calstar/ellie-ground/Calibration/Flow Meter Calibration Files/MatLabCdMeasurementCalc/Oct32022CdTest/OCt32022CdCalcr1.xls

Time(ms) | PT 2 | PT 3 | PT 4 | volume flow (m^3/s) | break Interval | mass flow (kg/s) | Cd Value | Reynolds Num
2075 | 137895.15 | 101352.93 | 0 | 0 | 1050 | 0 | 0 | 0
3125 | 137895.15 | 101352.93 | 0 | 0 | 1050 | 0 | 0 | 0
4175 | 137895.15 | 101352.93 | 0 | 0 | 1050 | 0 | 0 | 0
4503 | 137895.15 | 101352.93 | 0 | 3.499239381e-06 | 328 | 0.003499239381 | 0 | 1.292703316e-07
4566 | 137895.15 | 101352.93 | 0 | 9.917990395e-06 | 63 | 0.009917990395 | 0 | 3.663944554e-07
4633 | 137895.15 | 101352.93 | 0 | 1.789682177e-05 | 67 | 0.01789682177 | 0 | 6.611517056e-07
4695 | 137895.15 | 101352.93 | 0 | 2.812016238e-05 | 62 | 0.02812016238 | 0 | 1.038826533e-06
4752 | 137895.15 | 101352.93 | 0 | 3.895757001e-05 | 57 | 0.03895757001 | 0 | 1.439186476e-06
4806 | 137895.15 | 101352.93 | 0 | 4.967108693e-05 | 54 | 0.04967108693 | 0 | 1.834969597e-06
4859 | 137895.15 | 101352.93 | 0 | 5.973249429e-05 | 53 | 0.05973249429 | 0 | 2.206662221e-06
4914 | 137895.15 | 101352.93 | 0 | 7.192731323e-05 | 55 | 0.07192731323 | 0 | 2.657168207e-06
4968 | 137895.15 | 101352.93 | 0 | 7.931766371e-05 | 54 | 0.07931766371 | 0 | 2.930185556e-06
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
