calstar/ellie-ground/Calibration/Flow Meter Calibration Files/MatLabCdMeasurementCalc/Oct32022CdTest/OCt32022CdCalcr2.xls

Time(ms) | PT 2 | PT 3 | PT 4 | volume flow (m^3/s) | break Interval | mass flow (kg/s) | Cd Value | Reynolds Num
4075 | 137895.15 | 101352.93 | 0 | 0 | 2050 | 0 | 0 | 0
6125 | 137895.15 | 101352.93 | 0 | 0 | 2050 | 0 | 0 | 0
8175 | 137895.15 | 101352.93 | 0 | 0 | 2050 | 0 | 0 | 0
8641 | 137895.15 | 101352.93 | 0 | 4.409600475e-05 | 466 | 0.04409600475 | 0 | 1.629012633e-06
8716 | 137895.15 | 101352.93 | 0 | 0.0001655294417 | 75 | 0.1655294417 | 0 | 6.1150563e-06
8787 | 137895.15 | 101352.93 | 0 | 0.0002653648218 | 71 | 0.2653648218 | 0 | 9.803215721e-06
8850 | 137895.15 | 101352.93 | 0 | 0.0003489301191 | 63 | 0.3489301191 | 0 | 1.289031909e-05
8911 | 137895.15 | 101352.93 | 0 | 0.0004213509752 | 61 | 0.4213509752 | 0 | 1.556571996e-05
8973 | 137895.15 | 101352.93 | 0 | 0.0004833589514 | 62 | 0.4833589514 | 0 | 1.785644397e-05
9033 | 137895.15 | 101352.93 | 0 | 0.0005332515604 | 60 | 0.5332515604 | 0 | 1.969959712e-05
9091 | 137895.15 | 101352.93 | 0 | 0.0005587710277 | 58 | 0.5587710277 | 0 | 2.064234771e-05
9148 | 137895.15 | 101352.93 | 0 | 0.0005754865111 | 57 | 0.5754865111 | 0 | 2.125985794e-05
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
