calstar/ellie-ground/Calibration/Flow Meter Calibration Files/MatLabCdMeasurementCalc/Oct32022CdTest/OCt32022CdCalcr3.xls

Time(ms) | PT 2 | PT 3 | PT 4 | volume flow (m^3/s) | break Interval | mass flow (kg/s) | Cd Value | Reynolds Num
4075 | 137895.15 | 101352.93 | 0 | 0 | 2050 | 0 | 0 | 0
5894 | 137895.15 | 101352.93 | 0 | 4.142494664e-05 | 1819 | 5.260968223e-05 | 0.01015786496 | 1.943528386e-09
6062 | 137895.15 | 101352.93 | 0 | 3.997073106e-05 | 168 | 5.076282844e-05 | 0.009801274869 | 1.875301159e-09
6194 | 137895.15 | 101352.93 | 0 | 7.002451974e-05 | 132 | 8.893114007e-05 | 0.01717080342 | 3.285330529e-09
6299 | 137895.15 | 101352.93 | 0 | 0.0001073493863 | 105 | 0.0001363337207 | 0.02632328243 | 5.036496038e-09
6388 | 137895.15 | 101352.93 | 0 | 0.0001479260406 | 89 | 0.0001878660715 | 0.0362731365 | 6.940225208e-09
6471 | 137895.15 | 101352.93 | 0 | 0.0001819183298 | 83 | 0.0002310362788 | 0.04460842988 | 8.535036653e-09
6541 | 137895.15 | 101352.93 | 0 | 0.0002122346852 | 70 | 0.0002695380502 | 0.05204234276 | 9.957384828e-09
6612 | 137895.15 | 101352.93 | 0 | 0.0002406726788 | 71 | 0.000305654302 | 0.0590156601 | 1.129160617e-08
6684 | 137895.15 | 101352.93 | 0 | 0.0002612942636 | 72 | 0.0003318437148 | 0.0640723057 | 1.225910616e-08
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
