calstar/ellie-ground/Calibration/Flow Meter Calibration Files/MatLabCdMeasurementCalc/Sep102022CdTest/Sep102022CdCalcr1.xls

Time(ms) | PT 2 | PT 3 | PT 4 | volume flow (m^3/s) | break Interval | mass flow (kg/s) | Cd Value | Reynolds Num
2476 | 117210.87 | 101352.93 | 0 | 0 | 1050 | 0 | 0 | 0
3526 | 117210.87 | 101352.93 | 0 | 0 | 1050 | 0 | 0 | 0
4576 | 117210.87 | 101352.93 | 0 | 0 | 1050 | 0 | 0 | 0
5626 | 117210.87 | 101352.93 | 0 | 0 | 1050 | 0 | 0 | 0
6676 | 117210.87 | 101352.93 | 0 | 0 | 1050 | 0 | 0 | 0
7726 | 117210.87 | 101352.93 | 0 | 0 | 1050 | 0 | 0 | 0
8776 | 117210.87 | 101352.93 | 0 | 0 | 1050 | 0 | 0 | 0
9826 | 117210.87 | 101352.93 | 0 | 0 | 1050 | 0 | 0 | 0
10876 | 117210.87 | 101352.93 | 0 | 0 | 1050 | 0 | 0 | 0
11926 | 117210.87 | 101352.93 | 0 | 0 | 1050 | 0 | 0 | 0
12976 | 117210.87 | 101352.93 | 0 | 0 | 1050 | 0 | 0 | 0
14026 | 117210.87 | 101352.93 | 0 | 0 | 1050 | 0 | 0 | 0
15076 | 117210.87 | 101352.93 | 0 | 0 | 1050 | 0 | 0 | 0
16126 | 117210.87 | 101352.93 | 0 | 0 | 1050 | 0 | 0 | 0
17176 | 117210.87 | 101352.93 | 0 | 0 | 1050 | 0 | 0 | 0
18226 | 117210.87 | 101352.93 | 0 | 0 | 1050 | 0 | 0 | 0
19276 | 117210.87 | 101352.93 | 0 | 0 | 1050 | 0 | 0 | 0
20326 | 117210.87 | 101352.93 | 0 | 0 | 1050 | 0 | 0 | 0
21376 | 117210.87 | 101352.93 | 0 | 0 | 1050 | 0 | 0 | 0
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
