calstar/ellie-ground/PCB Design/ellie_board/EllieBoard.kicad_sch

## KiCad design PCB Design/ellie_board/EllieBoard.kicad_sch (2022-04-06)

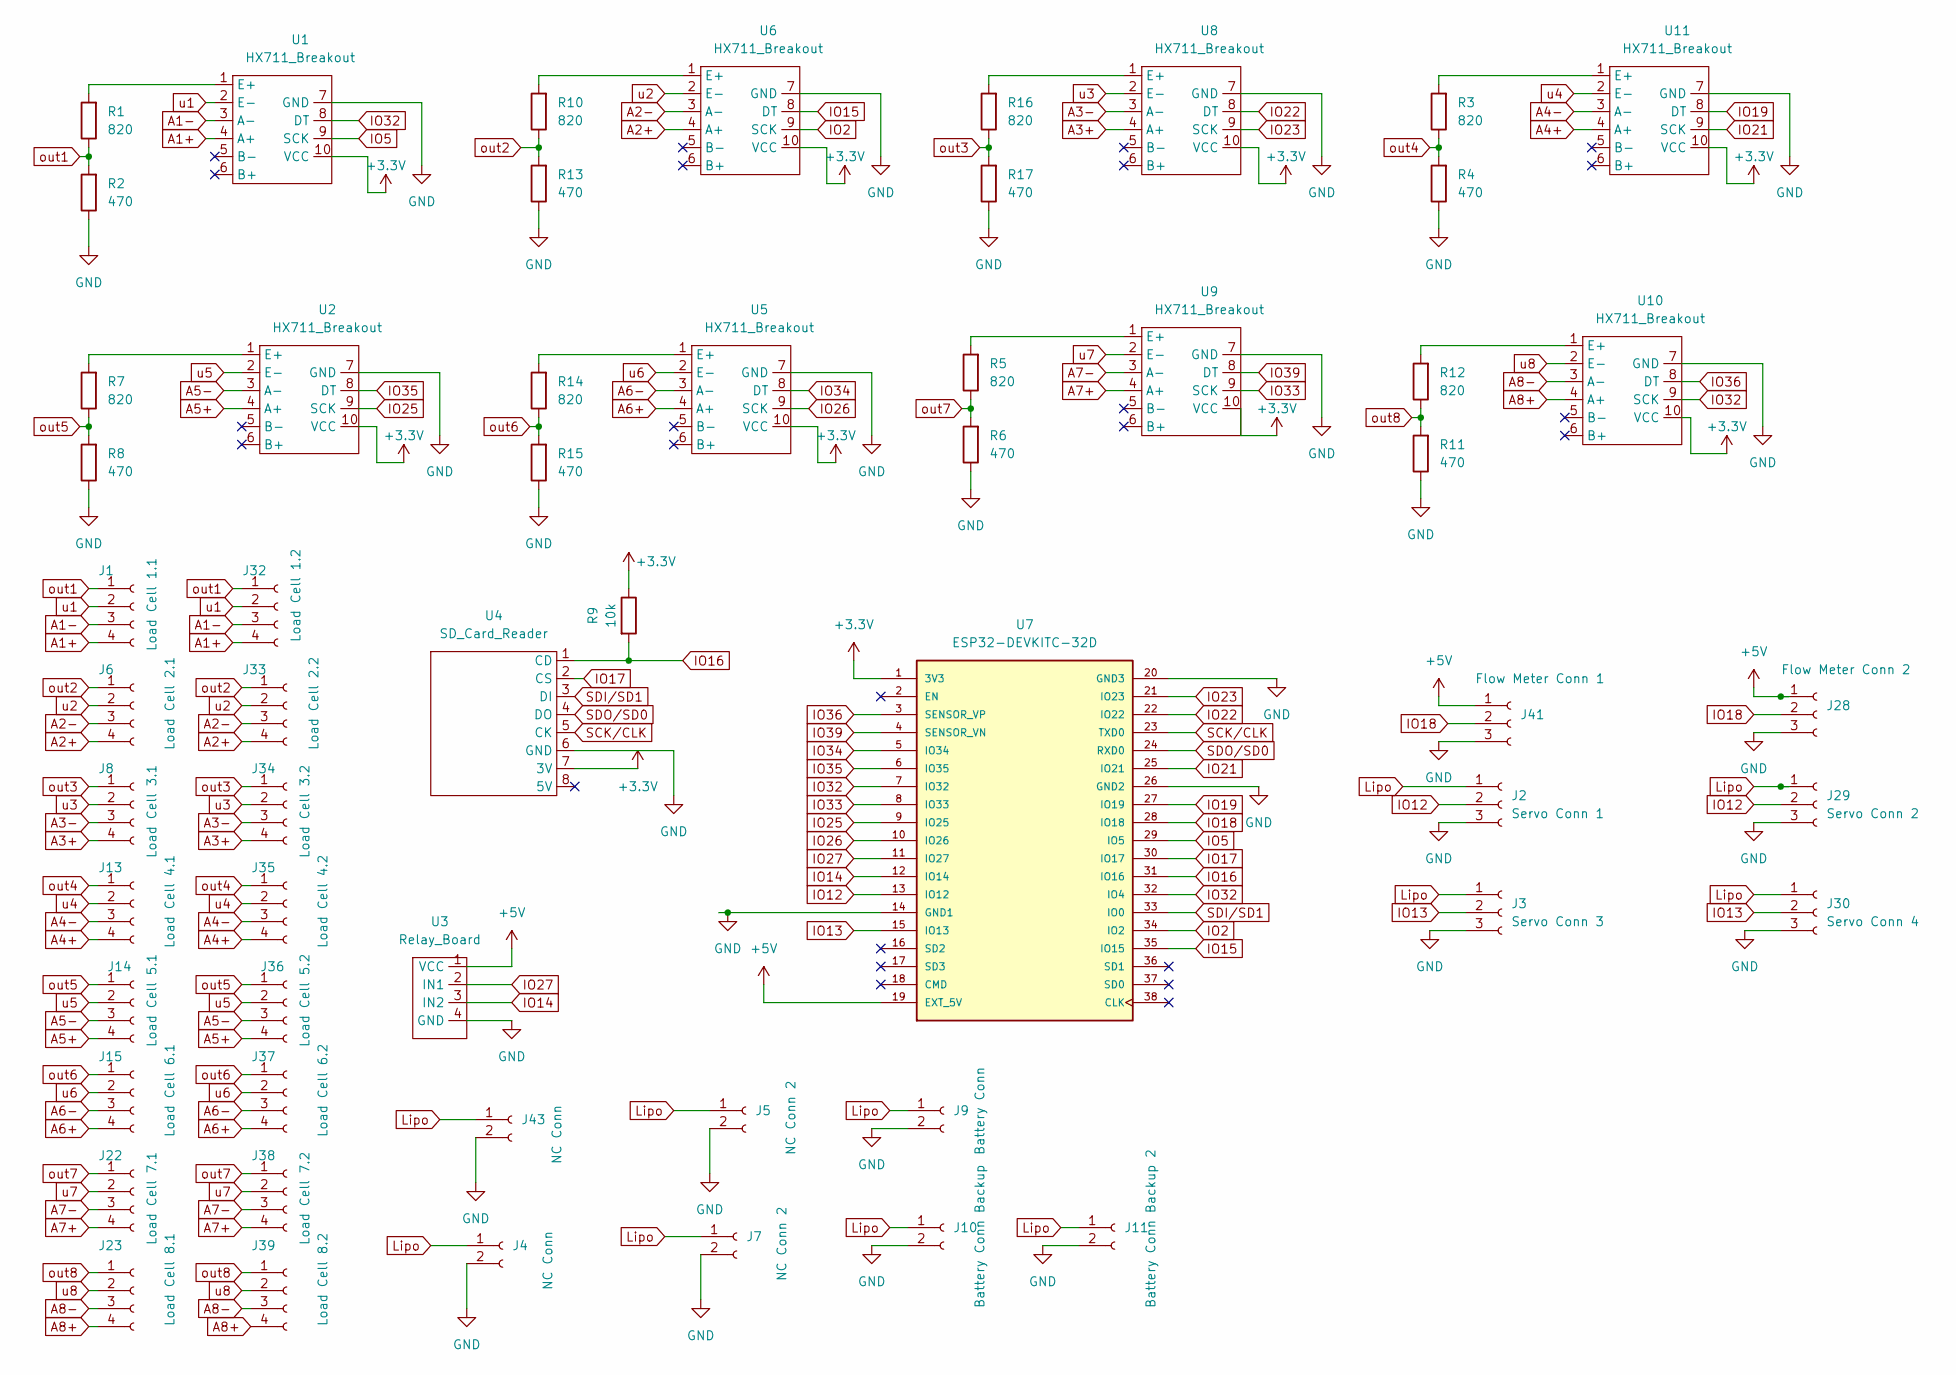
[picture p6: schematic EllieBoard.kicad_sch]

Parts:
J1: Load Cell 1.1; JST_XH_B4B-XH-AM_1x04_P2.50mm_Vertical
J2: Servo Conn 1; JST_XH_B3B-XH-AM_1x03_P2.50mm_Vertical
J3: Servo Conn 3; JST_XH_B3B-XH-AM_1x03_P2.50mm_Vertical
J4, J43: NC Conn; JST_XH_B2B-XH-AM_1x02_P2.50mm_Vertical
J5, J7: NC Conn 2; TerminalBlock_Phoenix_MPT-0,5-2-2.54_1x02_P2.54mm_Horizontal
J6: Load Cell 2.1; JST_XH_B4B-XH-AM_1x04_P2.50mm_Vertical
J8: Load Cell 3.1; JST_XH_B4B-XH-AM_1x04_P2.50mm_Vertical
J9: Battery Conn; DEANS
J10: Battery Conn Backup; JST_XH_B2B-XH-AM_1x02_P2.50mm_Vertical
J11: Battery Conn Backup 2; TerminalBlock_Phoenix_MPT-0,5-2-2.54_1x02_P2.54mm_Horizontal
J13: Load Cell 4.1; JST_XH_B4B-XH-AM_1x04_P2.50mm_Vertical
J14: Load Cell 5.1; JST_XH_B4B-XH-AM_1x04_P2.50mm_Vertical
J15: Load Cell 6.1; JST_XH_B4B-XH-AM_1x04_P2.50mm_Vertical
J22: Load Cell 7.1; JST_XH_B4B-XH-AM_1x04_P2.50mm_Vertical
J23: Load Cell 8.1; JST_XH_B4B-XH-AM_1x04_P2.50mm_Vertical
J28: Flow Meter Conn 2; TerminalBlock_Phoenix_MPT-0,5-3-2.54_1x03_P2.54mm_Horizontal
J29: Servo Conn 2; TerminalBlock_Phoenix_MPT-0,5-3-2.54_1x03_P2.54mm_Horizontal
J30: Servo Conn 4; TerminalBlock_Phoenix_MPT-0,5-3-2.54_1x03_P2.54mm_Horizontal
J32: Load Cell 1.2; TerminalBlock_Phoenix_MPT-0,5-4-2.54_1x04_P2.54mm_Horizontal
J33: Load Cell 2.2; TerminalBlock_Phoenix_MPT-0,5-4-2.54_1x04_P2.54mm_Horizontal
J34: Load Cell 3.2; TerminalBlock_Phoenix_MPT-0,5-4-2.54_1x04_P2.54mm_Horizontal
J35: Load Cell 4.2; TerminalBlock_Phoenix_MPT-0,5-4-2.54_1x04_P2.54mm_Horizontal
J36: Load Cell 5.2; TerminalBlock_Phoenix_MPT-0,5-4-2.54_1x04_P2.54mm_Horizontal
J37: Load Cell 6.2; TerminalBlock_Phoenix_MPT-0,5-4-2.54_1x04_P2.54mm_Horizontal
J38: Load Cell 7.2; TerminalBlock_Phoenix_MPT-0,5-4-2.54_1x04_P2.54mm_Horizontal
J39: Load Cell 8.2; TerminalBlock_Phoenix_MPT-0,5-4-2.54_1x04_P2.54mm_Horizontal
J41: Flow Meter Conn 1; JST_XH_B3B-XH-AM_1x03_P2.50mm_Vertical
R1, R3, R5, R7, R10, R12, R14, R16: 820; R_1206_3216Metric
R2, R4, R6, R8, R11, R13, R15, R17: 470; R_1206_3216Metric
R9: 10k; R_1206_3216Metric
U1, U2, U5, U6, U8, U9, U10, U11: HX711_Breakout; HX711_Breakout_Board
U3: Relay_Board; Relay_Breakout
U4: SD_Card_Reader; SD_Card_Breakout
U7: ESP32-DEVKITC-32D; MODULE_ESP32-DEVKITC-32D; PARTREV 4

Connections:
+3.3V: R9.1, U1.10 (VCC), U2.10 (VCC), U4.7 (3V), U5.10 (VCC), U6.10 (VCC), U7.1 (3V3), U8.10 (VCC), U9.10 (VCC), U10.10 (VCC), U11.10 (VCC)
+5V: J28.1, J41.1, U3.1 (VCC), U7.19 (EXT_5V)
A1+: J1.4, J32.4, U1.4 (A+)
A1-: J1.3, J32.3, U1.3 (A-)
A2+: J6.4, J33.4, U6.4 (A+)
A2-: J6.3, J33.3, U6.3 (A-)
A3+: J8.4, J34.4, U8.4 (A+)
A3-: J8.3, J34.3, U8.3 (A-)
A4+: J13.4, J35.4, U11.4 (A+)
A4-: J13.3, J35.3, U11.3 (A-)
A5+: J14.4, J36.4, U2.4 (A+)
A5-: J14.3, J36.3, U2.3 (A-)
A6+: J15.4, J37.4, U5.4 (A+)
A6-: J15.3, J37.3, U5.3 (A-)
A7+: J22.4, J38.4, U9.4 (A+)
A7-: J22.3, J38.3, U9.3 (A-)
A8+: J23.4, J39.4, U10.4 (A+)
A8-: J23.3, J39.3, U10.3 (A-)
GND: J2.3, J3.3, J4.2, J5.2, J7.2, J9.2, J10.2, J11.2, J28.3, J29.3, J30.3, J41.3, J43.2, R2.1, R4.1, R6.1, R8.1, R11.1, R13.1, R15.1, R17.1, U1.7 (GND), U2.7 (GND), U3.4 (GND), U4.6 (GND), U5.7 (GND), U6.7 (GND), U7.14 (GND1), U7.20 (GND3), U7.26 (GND2), U8.7 (GND), U9.7 (GND), U10.7 (GND), U11.7 (GND)
IO2: U6.9 (SCK), U7.34 (IO2)
IO5: U1.9 (SCK), U7.29 (IO5)
IO12: J2.2, J29.2, U7.13 (IO12)
IO13: J3.2, J30.2, U7.15 (IO13)
IO14: U3.3 (IN2), U7.12 (IO14)
IO15: U6.8 (DT), U7.35 (IO15)
IO16: R9.2, U4.1 (CD), U7.31 (IO16)
IO17: U4.2 (CS), U7.30 (IO17)
IO18: J28.2, J41.2, U7.28 (IO18)
IO19: U7.27 (IO19), U11.8 (DT)
IO21: U7.25 (IO21), U11.9 (SCK)
IO22: U7.22 (IO22), U8.8 (DT)
IO23: U7.21 (IO23), U8.9 (SCK)
IO25: U2.9 (SCK), U7.9 (IO25)
IO26: U5.9 (SCK), U7.10 (IO26)
IO27: U3.2 (IN1), U7.11 (IO27)
IO32: U1.8 (DT), U7.7 (IO32), U7.32 (IO4), U10.9 (SCK)
IO33: U7.8 (IO33), U9.9 (SCK)
IO34: U5.8 (DT), U7.5 (IO34)
IO35: U2.8 (DT), U7.6 (IO35)
IO36: U7.3 (SENSOR_VP), U10.8 (DT)
IO39: U7.4 (SENSOR_VN), U9.8 (DT)
Lipo: J2.1, J3.1, J4.1, J5.1, J7.1, J9.1, J10.1, J11.1, J29.1, J30.1, J43.1
unnamed: R1.2, U1.1 (E+)
unnamed: R3.2, U11.1 (E+)
unnamed: R5.2, U9.1 (E+)
unnamed: R7.2, U2.1 (E+)
unnamed: R10.2, U6.1 (E+)
unnamed: R12.2, U10.1 (E+)
unnamed: R14.2, U5.1 (E+)
unnamed: R16.2, U8.1 (E+)
SCK/CLK: U4.5 (CK), U7.23 (TXD0)
SDI/SD1: U4.3 (DI), U7.33 (IO0)
SDO/SD0: U4.4 (DO), U7.24 (RXD0)
out1: J1.1, J32.1, R1.1, R2.2
out2: J6.1, J33.1, R10.1, R13.2
out3: J8.1, J34.1, R16.1, R17.2
out4: J13.1, J35.1, R3.1, R4.2
out5: J14.1, J36.1, R7.1, R8.2
out6: J15.1, J37.1, R14.1, R15.2
out7: J22.1, J38.1, R5.1, R6.2
out8: J23.1, J39.1, R11.2, R12.1
u1: J1.2, J32.2, U1.2 (E-)
u2: J6.2, J33.2, U6.2 (E-)
u3: J8.2, J34.2, U8.2 (E-)
u4: J13.2, J35.2, U11.2 (E-)
u5: J14.2, J36.2, U2.2 (E-)
u6: J15.2, J37.2, U5.2 (E-)
u7: J22.2, J38.2, U9.2 (E-)
u8: J23.2, J39.2, U10.2 (E-)
