calstar/ellie-ground/sensor_board/sensor_board.kicad_sch

## KiCad design sensor_board/sensor_board.kicad_sch (2022-04-04)

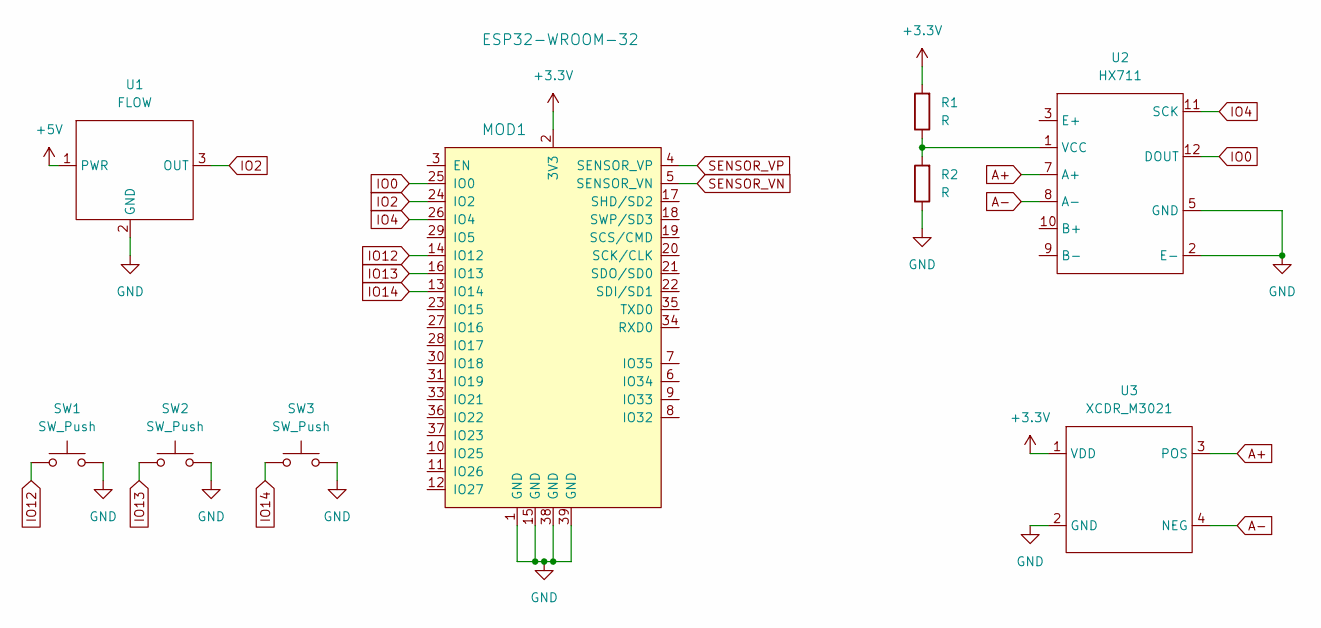
[picture p7: schematic sensor_board.kicad_sch]

Parts:
MOD1: ESP32-WROOM-32; ESP32-WROOM-32D; MPN ESP32-WROOM-32; Digi-Key_PN 1904-1010-1-ND
R1, R2: R
SW1, SW2, SW3: SW_Push
U1: FLOW
U2: HX711
U3: XCDR_M3021

Connections:
+3.3V: MOD1.2 (3V3), R1.2, U3.1 (VDD)
+5V: U1.1 (PWR)
A+: U2.7 (A+), U3.3 (POS)
A-: U2.8 (A-), U3.4 (NEG)
GND: MOD1.1 (GND), MOD1.15 (GND), MOD1.38 (GND), MOD1.39 (GND), R2.1, SW1.2, SW2.2, SW3.2, U1.2 (GND), U2.2 (E-), U2.5 (GND), U3.2 (GND)
IO0: MOD1.25 (IO0), U2.12 (DOUT)
IO2: MOD1.24 (IO2), U1.3 (OUT)
IO4: MOD1.26 (IO4), U2.11 (SCK)
IO12: MOD1.14 (IO12), SW1.1
IO13: MOD1.16 (IO13), SW2.1
IO14: MOD1.13 (IO14), SW3.1
unnamed: R1.1, R2.2, U2.1 (VCC)
SENSOR_VN: MOD1.5 (SENSOR_VN)
SENSOR_VP: MOD1.4 (SENSOR_VP)
