calstar/ellie-ground/Aurduino/Main.Stable/COMBoard/COMBoard.ino

#include <esp_now.h>
#include <WiFi.h>
#include <ESP32Servo.h>
#include <Wire.h>
#include <Arduino.h>
#include "HX711.h"


int servo1ClosedPosition = 100;
int servo1OpenPosition = 0;
int servo2ClosedPosition = 130;
int servo2OpenPosition = 20;
//EH VENT SEFRVO 1 =180

float pressTime = 0;
const int buttonpin1 = 19;
//const int buttonpin1 = 27;
const int buttonpin2 = 17;
const int igniterIndicator = 16;
const int firePin = 21; //SET PIN NUMBER BUTTON

const int pin6 = 4;
const int LEDpin = 23;
const int servo1Open = 22;//SET PIN NUMBER BASED ON SOLDERING//
const int servo2Open = 14;//SET PIN NUMBER BASED ON SOLDERING//
const int DAQIndicator = 25;//SET PIN NUMBER BASED ON SOLDERING//
const int COMIndicator = 5;//SET PIN NUMBER BASED ON SOLDERING//


String success;
String message;
int servo1_curr = servo1ClosedPosition;
int servo2_curr = servo2ClosedPosition;
float incomingS1 = 0;
float incomingS2 = 0;
float incomingPT1 = 0;
float incomingPT2 = 0;
float incomingPT3 = 0;
float incomingPT4 = 0;
float incomingFM = 0;
float incomingLC1 = 0;
float incomingLC2 = 0;
float incomingLC3 = 0;
esp_now_peer_info_t peerInfo;
bool pressed1 = false;
bool pressed2 = false;
bool pressed3 = false;

// SET FOR ACTIVE MODE //
bool hotfire = true;
//SET IF PLOTTING WITH MATLAB OR NOT. SERVO MANUAL CONTROL AND
//MATLAB PLOTTING ARE NOT COMPATIBLE DUE TO USING THE SAME SERIAL
//INPUT. IF TRUE, PLOTTING ENABLED. IF FALSE, MANUAL CONTROL ENABLED
bool MatlabPlot = true;


float button1Time = 0;
float currTime = 0;
float loopTime = 0;

float receiveTimeDAQ = 0;
float receiveTimeCOM = 0;

const int delayOpenServoTime = 250;
const int servoOnTime = 1500;
const int delayCloseServoTime = 0;

//for blinking LED during Data Collection
int x = 1;
unsigned long t1;
unsigned long t2;

int state = 0;
//

//DAQ Breadboard {0x24, 0x62, 0xAB, 0xD2, 0x85, 0xDC}
//DAQ Protoboard {0x0C, 0xDC, 0x7E, 0xCB, 0x05, 0xC4}
//NON BUSTED DAQ {0x7C, 0x9E, 0xBD, 0xD8, 0xFC, 0x14}
// uint8_t broadcastAddress[] = {0x7C, 0x9E, 0xBD, 0xD8, 0xFC, 0x14}; //change to new Mac Address

uint8_t broadcastAddress[] = {0x30, 0xC6, 0xF7, 0x2A, 0x28, 0x04};
//Structure example to send data
//Must match the receiver structure
typedef struct struct_message {
    float pt1;
    float pt2;
    float pt3;
    float pt4;
    float lc1;
    float lc2;
    float lc3;
    float fm;
    int S1;
    int S2;
    int S1S2;
    boolean I;
} struct_message;

// Create a struct_message called Readings to recieve sensor readings remotely
struct_message incomingReadings;

// Create a struct_message to send commands
struct_message Commands;

//
void OnDataSent(const uint8_t *mac_addr, esp_now_send_status_t status) {
 // Serial.print("\r\nLast Packet Send Status:\t");
 // Serial.println(status == ESP_NOW_SEND_SUCCESS ? "Delivery Success" : "Delivery Fail");
  if (status == 0){
    success = "Delivery Success :)";
    digitalWrite(DAQIndicator, HIGH);
    receiveTimeDAQ = millis();
  }
  else{
    success = "Delivery Fail :(";
    digitalWrite(DAQIndicator, LOW);
  }

}

void OnDataRecv(const uint8_t * mac, const uint8_t *incomingData, int len) {
  memcpy(&incomingReadings, incomingData, sizeof(incomingReadings));
 // Serial.print("Bytes received: ");
  // Serial.println(len);
  incomingPT1 = incomingReadings.pt1;
  incomingPT2 = incomingReadings.pt2;
  incomingPT3 = incomingReadings.pt3;
  incomingPT4 = incomingReadings.pt4;
  incomingFM = incomingReadings.fm;
  incomingLC1 = incomingReadings.lc1;
  incomingLC2 = incomingReadings.lc2;
  incomingLC3 = incomingReadings.lc3;
  incomingS1 = incomingReadings.S1;
  incomingS2 = incomingReadings.S2;
  digitalWrite(COMIndicator, HIGH);
  receiveTimeCOM = millis();
  // Serial.println("Data received");

}

void printLine(String string) {
  // a = 10;
  Serial.println(string);
}

void setup() {
  Commands.S1 = servo1ClosedPosition;
  Commands.S2 = servo2ClosedPosition;
  // put your setup code here, to run once:
  Serial.begin(115200);
  pinMode(buttonpin1,INPUT);
  pinMode(buttonpin2, INPUT);
  pinMode(igniterIndicator,INPUT);
  pinMode(firePin, INPUT);

  pinMode(LEDpin, OUTPUT);
  pinMode(servo1Open, OUTPUT);
  pinMode(servo2Open, OUTPUT);
  pinMode(DAQIndicator, OUTPUT);
  pinMode(COMIndicator, OUTPUT);
  pinMode(pin6, OUTPUT);

  digitalWrite(LEDpin,LOW);
  digitalWrite(servo1Open, LOW);
  digitalWrite(servo2Open, LOW);
  digitalWrite(DAQIndicator, LOW);
  digitalWrite(COMIndicator, LOW);
  digitalWrite(pin6, LOW);


  //set device as WiFi station
  WiFi.mode(WIFI_STA);

  //initialize ESP32
   if (esp_now_init() != ESP_OK) {
    //Serial.println("Error initializing ESP-NOW");
    return;
  }
   // Once ESPNow is successfully Init, we will register for Send CB to
  // get the status of Trasnmitted packet
  esp_now_register_send_cb(OnDataSent);

  // Register peer
  memcpy(peerInfo.peer_addr, broadcastAddress, 6);
  peerInfo.channel = 0;
  peerInfo.encrypt = false;

  // Add peer
  if (esp_now_add_peer(&peerInfo) != ESP_OK){
    //Serial.println("Failed to add peer");
    return;
  }
  // Register for a callback function that will be called when data is received
  esp_now_register_recv_cb(OnDataRecv);

}


void loop() {
  message = "";
  // put your main code here, to run repeatedly:
  // STATES:
  // 0 = RESTING LED dark
  // 1 = ARMED LED Bright
  // 2 = ACTUATE VALVES ON PRE_SET PARAMETERS (IF USING MATLAB) LED Blinking
  //     READY FOR SERVO VALVE ANGLE INPUTS (IN FORM angle1,angle2)

// Serial.println(state);
  switch (state) {
    case 0:
//      Serial.println("State 0");
      //Serial.println("IN CASE 0");
      Commands.S1 = servo1ClosedPosition;
      Commands.S2 = servo2ClosedPosition;
      Commands.S1S2 = 0;
      //Serial.println("State 0");

      digitalWrite(LEDpin, LOW);
      digitalWrite(pin6, LOW);
      //digitalWrite(servo1Open, HIGH);
      //digitalWrite(servo2Open, HIGH);
      pressed1 = digitalRead(buttonpin1);
      currTime = millis();
      if (pressed1 && ((currTime - button1Time) > 1000)) {
        state = 1;
        button1Time = currTime;
        // Serial.println("State 1");
        // Serial.println("BUTTON 1 GOOD");
      }
      if ((millis() - receiveTimeDAQ) > 50) {
        digitalWrite(DAQIndicator, LOW);
      }
      if ((millis() - receiveTimeCOM) > 50) {
        digitalWrite(COMIndicator, LOW);
      }
      break;
    case 1:
      //Serial.println("State 1");
      //Serial.println("IN CASE 1");
      digitalWrite(LEDpin, HIGH);
      //Serial.println("State 1");
      pressed2 = digitalRead(buttonpin2);
      pressed3 = digitalRead(buttonpin1);
      currTime = millis();
      if (pressed2) {
        if (hotfire) {
          state = 4;
        } else {
          state = 2;
      }
        // Serial.println("State 2");
      }
      if (pressed3 && ((currTime - button1Time) > 1000)) {
        button1Time = currTime;
        state = 0;
        // Serial.println("State 0");
      }
      if ((millis() - receiveTimeDAQ) > 50) {
        digitalWrite(DAQIndicator, LOW);
      }
      if ((millis() - receiveTimeCOM) > 50) {
        digitalWrite(COMIndicator, LOW);
      }
      break;
    case 2:
    //  Serial.println("State 2");
      //Serial.println("IN CASE 2");
      if (MatlabPlot) {
        Commands.S1 = 90 - servo1_curr;
        Commands.S2 = 90 - servo2_curr;
        servo1_curr = 90 - servo1_curr;
        servo2_curr = 90 - servo2_curr;
        pressTime = millis();
        digitalWrite(pin6, HIGH);

        while (millis() - pressTime <= 5000) {

          t2=millis();
          if (t2-t1 >=100){
              x=1-x;
              t1=millis();
              digitalWrite(LEDpin,x);
              // Serial.print(t1);
            }

          pressed3 = digitalRead(buttonpin1);
          if (pressed3) {
            state = 0;
            break;
          }
          if (state == 3) {
            break;
          }
          if ((millis() - receiveTimeDAQ) > 50) {
            digitalWrite(DAQIndicator, LOW);
          }
          if ((millis() - receiveTimeCOM) > 50) {
            digitalWrite(COMIndicator, LOW);
          }

          if ((millis() - loopTime) >= 50) {
            esp_err_t result = esp_now_send(broadcastAddress, (uint8_t *) &Commands, sizeof(Commands));
            if (result != ESP_OK) {
              break;
            // Serial.println("Sent with success");
            }
            //else {
              //Serial.println("Error sending the data");
            //}
            loopTime = millis();
           // Serial.print(loopTime);
           // Serial.print(" ");
            // Print the flow rate for this second in litres / minute
            // Serial.print("Flow rate: ");
            //Serial.print(incomingFM);  // Print the integer part of the variable
            //Serial.print("L/min");
            //Serial.print(" ");       // Print tab space

           //PT TEST
            //Serial.print("Output Pressures: ");
            message = "";
            message.concat(incomingPT1);
            message.concat(" ");
            message.concat(incomingPT2);
            message.concat(" ");
            message.concat(incomingPT3);
            message.concat(" ");
            message.concat(incomingPT4);
            message.concat(" ");
            message.concat(incomingLC1);
            message.concat(" ");
            message.concat(incomingFM);

            printLine(message);

            //Serial.println("psi / ");

          //  Serial.print(" ");       // Print tab space

          // FM Test


            // Serial.print(" ");

            //Serial.println("Commands Follow");
            // Serial.print(Commands.S1);
            // Serial.print(" ");
            // Serial.println(Commands.S2);
             // Print the cumulative total of litres flowed since starting
            //Serial.print("Output Liquid Quantity: ");
             //Serial.print(totalMilliLitres);
             //Serial.print("mL / ");
             //Serial.print(totalMilliLitres / 1000);
             //Serial.print("L");
             //Serial.print("\t");       // Print tab space

           //LC TEST

           //Serial.print("Load Cell Stuff:");
           //Serial.print(incomingLC1);
           //Serial.print(incomingLC2);
           //Serial.print(incomingLC3);

           //delay(50); //delay of 50 optimal for recieving and transmitting
         }
        }

      } else {
        while (!Serial.available()) {
          pressed3 = digitalRead(buttonpin1);
          Serial.print(pressed3);
          delay(5);
          if ((millis() - receiveTimeDAQ) > 50) {
            digitalWrite(DAQIndicator, LOW);
          }
          if ((millis() - receiveTimeCOM) > 50) {
            digitalWrite(COMIndicator, LOW);
          }
          esp_err_t result = esp_now_send(broadcastAddress, (uint8_t *) &Commands, sizeof(Commands));
            if (result != ESP_OK) {
              break;
            // Serial.println("Sent with success");
            }
            //else {
              //Serial.println("Error sending the data");
            //}
          if (pressed3) {
            state = 0;
            // Serial.println("State 0");
            break;}  //waiting for inputs
          }
        String angles = Serial.readString();
        int index = angles.indexOf(",");
        String readAngle1 = angles.substring(0, index);
        String readAngle2 = angles.substring(index+1, angles.length());
        if (angles.length() >= 3) {
          Serial.println(readAngle1);
          Serial.println(readAngle2);
          Commands.S1 = readAngle1.toInt();
          Commands.S2 = readAngle2.toInt();
          if (Commands.S1 == servo1ClosedPosition) {
            digitalWrite(servo1Open, LOW);
          } else {
            digitalWrite(servo1Open, HIGH);
          }

          if (Commands.S2 == servo2ClosedPosition) {
            digitalWrite(servo2Open, LOW);
          } else {
            digitalWrite(servo2Open, HIGH);
          }
          esp_err_t result = esp_now_send(broadcastAddress, (uint8_t *) &Commands, sizeof(Commands));
          if (result != ESP_OK) {
              break;
            // Serial.println("Sent with success");
            }
            //else {
              //Serial.println("Error sending the data");
            //}

        }

      }
      break;
     case 3:
    //  Serial.println("State 3");
      Commands.S1 = servo1ClosedPosition;
      Commands.S2 = servo2ClosedPosition;
      digitalWrite(DAQIndicator, LOW);
      digitalWrite(COMIndicator, LOW);
      digitalWrite(servo1Open, LOW);
      digitalWrite(servo2Open, LOW);
      if ((millis() - receiveTimeDAQ) > 50) {
        digitalWrite(DAQIndicator, LOW);
      }
      if ((millis() - receiveTimeCOM) > 50) {
        digitalWrite(COMIndicator, LOW);
      }

      break;
    case 4:
      //Serial.println("State 4");
      digitalWrite(pin6, HIGH);
      if (digitalRead(igniterIndicator)) {
        Commands.S1S2 = 99;
        Commands.S1 = servo1ClosedPosition;
        Commands.S2 = servo2ClosedPosition;
        esp_err_t result = esp_now_send(broadcastAddress, (uint8_t *) &Commands, sizeof(Commands));
        if (result != ESP_OK) {
            break;
          // Serial.println("Sent with success");
          }
        state = 5;
      }
      if (digitalRead(buttonpin1)) {
        state = 0;
      }
      if ((millis() - receiveTimeDAQ) > 100) {
        digitalWrite(DAQIndicator, LOW);
      }
      if ((millis() - receiveTimeCOM) > 100) {
        digitalWrite(COMIndicator, LOW);
      }
      break;
    case 5:
    //Serial.println("State 5");
    //Serial.println("State 5");
    // Serial.println(digitalRead(firePin));
      if (digitalRead(firePin)) {
        // Commands.I = true;
        Commands.S2 = servo2OpenPosition;
        // Serial.println(Commands.I);
        esp_err_t result = esp_now_send(broadcastAddress, (uint8_t *) &Commands, sizeof(Commands));
        float now = millis();
        float runningTime = millis();
        while (now - runningTime < delayOpenServoTime) {
          now = millis();
        }

//            Commands.S1 = servo1OpenPosition;

        // Serial.print("We are here");
        if (result != ESP_OK) {

          // Serial.println("Sent with success");
          break;
          }
        // Commands.I = false;
       Commands.S1 = servo1OpenPosition;
//       Commands.S2 = servo2OpenPosition;

        state = 0;
        result = esp_now_send(broadcastAddress, (uint8_t *) &Commands, sizeof(Commands));
        if (result != ESP_OK) {
            break;
          // Serial.println("Sent with success");
          }
        now = millis();
        runningTime = millis();
        digitalWrite(servo1Open, HIGH);
        digitalWrite(servo2Open, HIGH);
        while ((now - runningTime) <= servoOnTime) {
          now = millis();
  message = "";
  message.concat(millis());
  message.concat(" ");
  message.concat(incomingPT1);
  message.concat(" ");
  message.concat(incomingPT2);
  message.concat(" ");
  message.concat(incomingPT3);
  message.concat(" ");
  message.concat(incomingPT4);
  message.concat(" ");
  message.concat(incomingLC1);
  message.concat(" ");
  message.concat(incomingLC2);
  message.concat(" ");
  message.concat(incomingLC3);
  message.concat(" ");
  message.concat(incomingFM);
  message.concat(" ");
  message.concat(Commands.S1);
  message.concat(" ");
  message.concat(Commands.S2);
  message.concat(" ");
  message.concat(Commands.I);
  message.concat(" ");
  message.concat(Commands.S1S2);
  printLine(message);
  // result = esp_now_send(broadcastAddress, (uint8_t *) &Commands, sizeof(Commands));

        }
                digitalWrite(servo2Open, LOW);
        Commands.S2 = servo2ClosedPosition;
         result = esp_now_send(broadcastAddress, (uint8_t *) &Commands, sizeof(Commands));


        if (result != ESP_OK) {
            break;
//          Serial.println("Sent with success");
          }
        now = millis();
        runningTime = millis();
        while ((now- runningTime) <= delayCloseServoTime) {
          now = millis();
          message = "";
          message.concat(millis());
          message.concat(" ");
          message.concat(incomingPT1);
          message.concat(" ");
          message.concat(incomingPT2);
          message.concat(" ");
          message.concat(incomingPT3);
          message.concat(" ");
          message.concat(incomingPT4);
          message.concat(" ");
          message.concat(incomingLC1);
          message.concat(" ");
          message.concat(incomingLC2);
          message.concat(" ");
          message.concat(incomingLC3);
          message.concat(" ");
          message.concat(incomingFM);
          message.concat(" ");
          message.concat(Commands.S1);
          message.concat(" ");
          message.concat(Commands.S2);
          message.concat(" ");
          message.concat(Commands.I);
          message.concat(" ");
          message.concat(Commands.S1S2);

          printLine(message);
          now = millis();
        }

         digitalWrite(servo1Open, LOW);
        Commands.S1 = servo1ClosedPosition;

        result = esp_now_send(broadcastAddress, (uint8_t *) &Commands, sizeof(Commands));

        if (result != ESP_OK) {
            break;
          // Serial.println("Sent with success");
          }
//        digitalWrite(servo2Open, LOW);
      }
      if (digitalRead(buttonpin1)) {
        state = 0;
      }
      if ((millis() - receiveTimeDAQ) > 50) {
        digitalWrite(DAQIndicator, LOW);
      }
      if ((millis() - receiveTimeCOM) > 50) {
        digitalWrite(COMIndicator, LOW);
      }

    delay(30);
  }

  message = "";
  message.concat(millis());
  message.concat(" ");
  message.concat(incomingPT1);
  message.concat(" ");
  message.concat(incomingPT2);
  message.concat(" ");
  message.concat(incomingPT3);
  message.concat(" ");
  message.concat(incomingPT4);
  message.concat(" ");
  message.concat(incomingLC1);
  message.concat(" ");
  message.concat(incomingLC2);
  message.concat(" ");
  message.concat(incomingLC3);
  message.concat(" ");
  message.concat(incomingFM);
  message.concat(" ");
  message.concat(Commands.S1);
  message.concat(" ");
  message.concat(Commands.S2);
  message.concat(" ");
  message.concat(Commands.I);
  message.concat(" ");
  message.concat(Commands.S1S2);

  printLine(message);

  esp_err_t result = esp_now_send(broadcastAddress, (uint8_t *) &Commands, sizeof(Commands));


}
